abferguson/Park-Assist-with-Thingsboard-and-Telegram/KiCAD Files/Park Assist v2.kicad_sch

## KiCad design KiCAD Files/Park Assist v2.kicad_sch (2022-04-27)

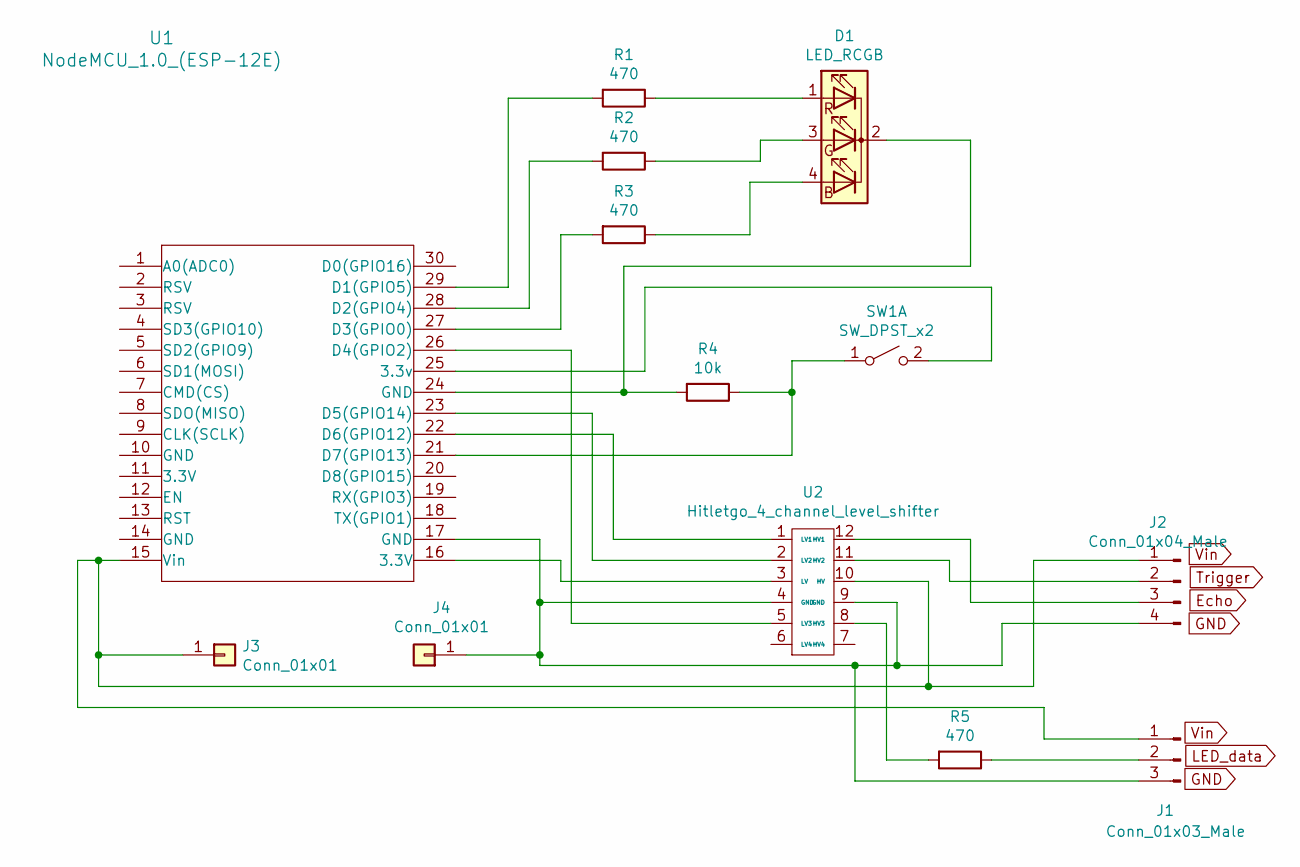
[picture p2: schematic Park Assist v2.kicad_sch]

Parts:
D1: LED_RCGB; LED_D5.0mm-4_RGB
J1: Conn_01x03_Male; PinHeader_1x03_P2.00mm_Vertical
J2: Conn_01x04_Male; PinHeader_1x04_P2.00mm_Vertical
J3: Conn_01x01; SolderWire-0.5sqmm_1x01_D0.9mm_OD2.1mm
J4: Conn_01x01; Pin_D1.0mm_L10.0mm
R1, R2, R3, R5: 470; R_Axial_DIN0207_L6.3mm_D2.5mm_P7.62mm_Horizontal
R4: 10k; R_Axial_DIN0207_L6.3mm_D2.5mm_P7.62mm_Horizontal
SW1: SW_DPST_x2; SW_PUSH_6mm
U1: NodeMCU_1.0_(ESP-12E); Tony-NodeMCU
U2: Hitletgo_4_channel_level_shifter; DIP-12_W10.16mm

Connections:
unnamed: D1.1 (RA), R1.1
unnamed: D1.2 (K), R4.2, U1.24 (GND)
unnamed: D1.3 (GA), R2.1
unnamed: D1.4 (BA), R3.1
unnamed: J1.1, J2.1, J3.1, U1.15 (Vin), U2.10 (HV)
unnamed: J1.2, R5.1
unnamed: J1.3, J2.4, J4.1, U1.17 (GND), U2.4 (GND), U2.9 (GND)
unnamed: J2.2, U2.11 (HV2)
unnamed: J2.3, U2.12 (HV1)
unnamed: R1.2, U1.29 (D1(GPIO5))
unnamed: R2.2, U1.28 (D2(GPIO4))
unnamed: R3.2, U1.27 (D3(GPIO0))
unnamed: R4.1, SW1.1 (A), U1.21 (D7(GPIO13))
unnamed: R5.2, U2.8 (HV3)
unnamed: SW1.2 (B), U1.25 (3.3v)
unnamed: U1.16 (3.3V), U2.3 (LV)
unnamed: U1.22 (D6(GPIO12)), U2.1 (LV1)
unnamed: U1.23 (D5(GPIO14)), U2.2 (LV2)
unnamed: U1.26 (D4(GPIO2)), U2.5 (LV3)
