abferguson/Park-Assist-with-Thingsboard-and-Telegram/Code/credentials.h

const char ssid[] = "your wifi SSID here";
const char wifiPassword[] = "wifi password";

const char unitName[] = "Mazda 3 Park Assist";
const char nodeName[] = "ferg_park_assist_mazda"; // Local WiFi host name
const char OTAname[] = "park_assist_mazda"; // OTA update name

const char thingsboardServer[] = "192.168.1.107";

const char deviceToken[] = "Thingsboard device access token here"; // Mazda park assist device token

// Thingsboard address and attribute stuff for getting client data
const char server[] = "http://192.168.1.107:8080/api/v1/";
const char clientKeys[] = "/attributes?clientKeys=bootTime,enablenotify,notified,notifyerror";

const char ntpServer[] = "us.pool.ntp.org";

// Telegram stuff
const char telegram_api[] = "Telegram API token here"; // mazda park assist
const char chat_id[] = "Telegram chat ID here";
